rsilvers129/7-Segment/IMG_0554.jpg

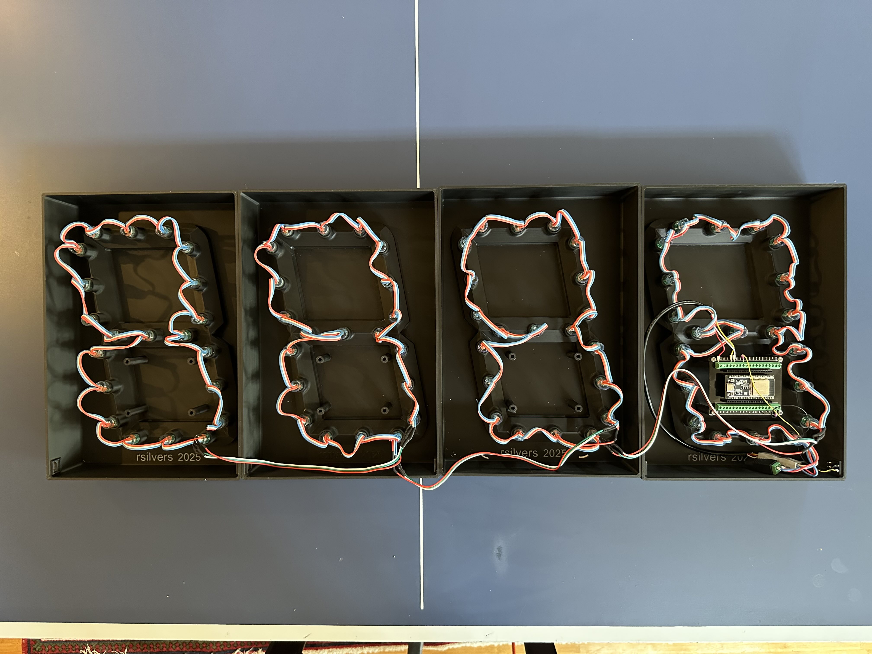
IMG_0554.jpg
