rsilvers129/7-Segment/IMG_0555.jpg

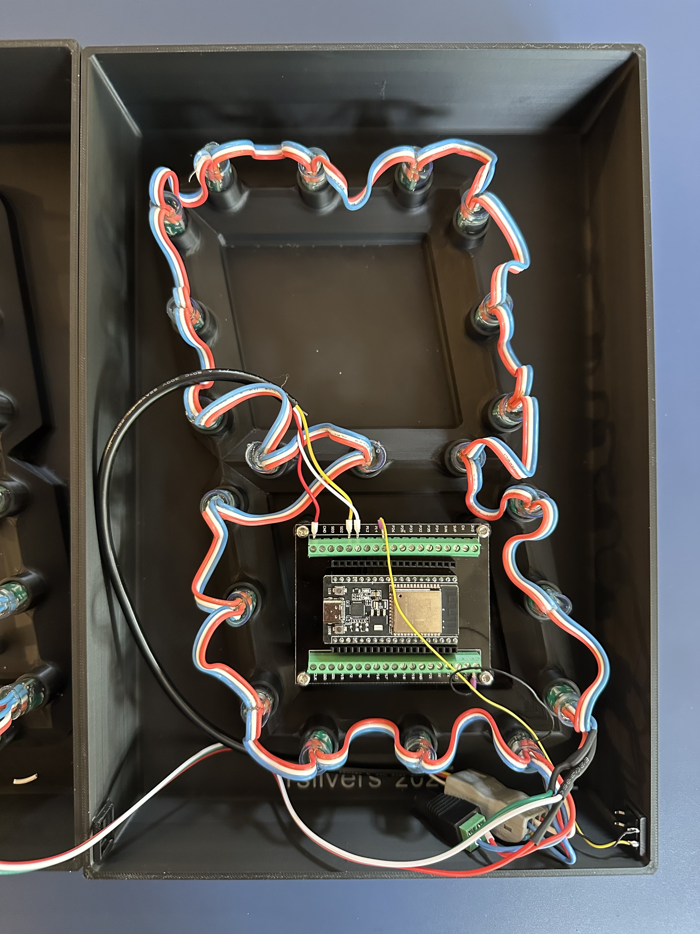
IMG_0555.jpg
